FabLabUTFSM/EPP-COVID19/Imagenes/muestra.jpeg

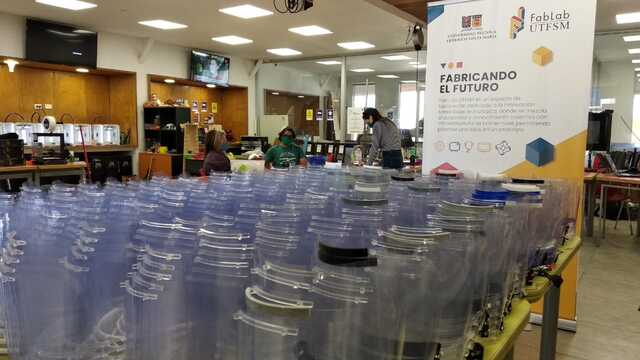
Imagenes/muestra.jpeg
